neoxelox/HAM/schematics/HAM-BLINDS/ham-blinds_schematic_root.png

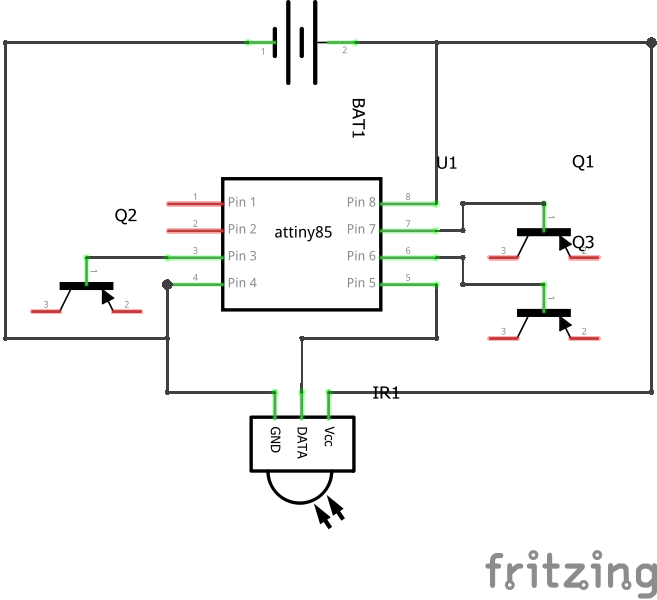
schematics/HAM-BLINDS/ham-blinds_schematic_root.png
