neoxelox/HAM/schematics/HAM-EXT/ham-ext_schematic.png

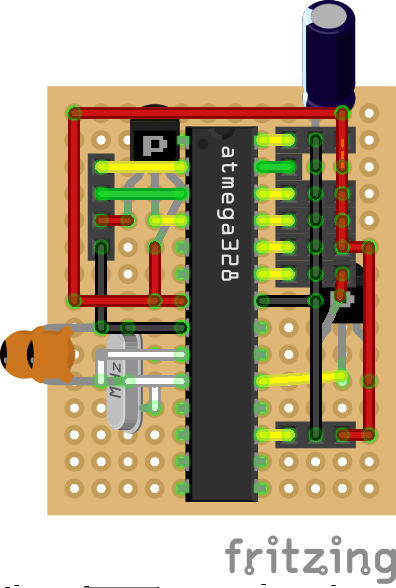
schematics/HAM-EXT/ham-ext_schematic.png
