neoxelox/HAM/schematics/HAM-GAS/ham-gas_schematic.png

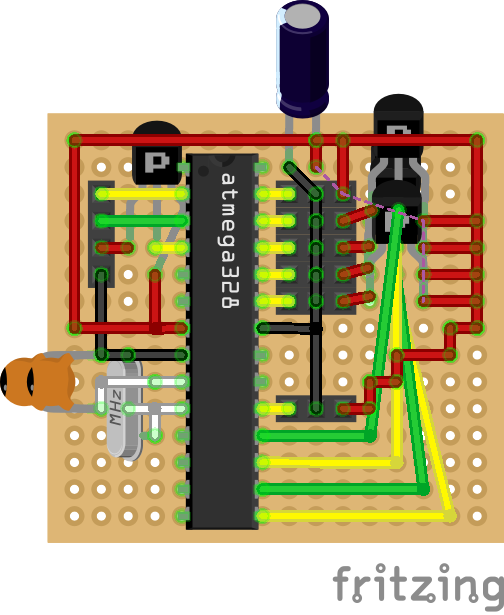
schematics/HAM-GAS/ham-gas_schematic.png
