neoxelox/HAM/schematics/HAM-HUB/ham-hub_schematic-covered.png

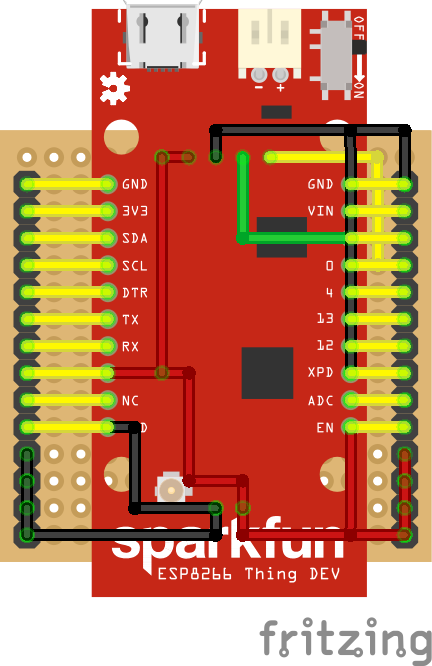
schematics/HAM-HUB/ham-hub_schematic-covered.png
