neoxelox/HAM/schematics/HAM-HUB/ham-hub_schematic-uncovered.png

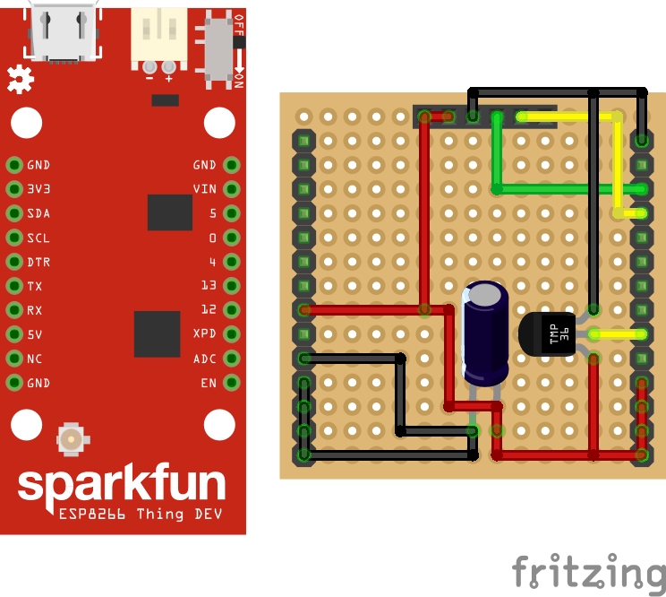
schematics/HAM-HUB/ham-hub_schematic-uncovered.png
