neoxelox/HAM/schematics/HAM-PEEPHOLE/ham-peephole_schematic.png

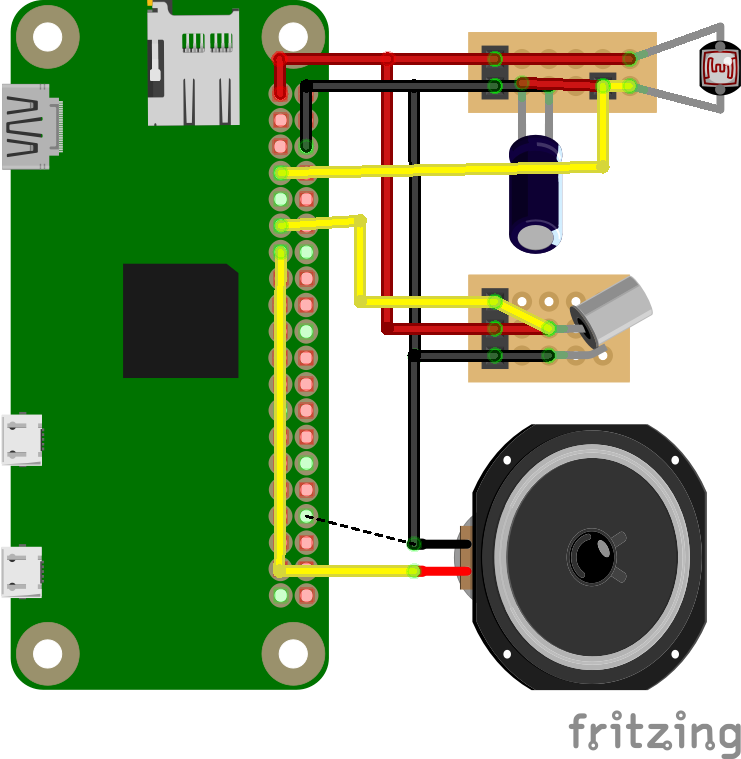
schematics/HAM-PEEPHOLE/ham-peephole_schematic.png
