neoxelox/HAM/schematics/HAM-RDT/ham-rdt_schematic.png

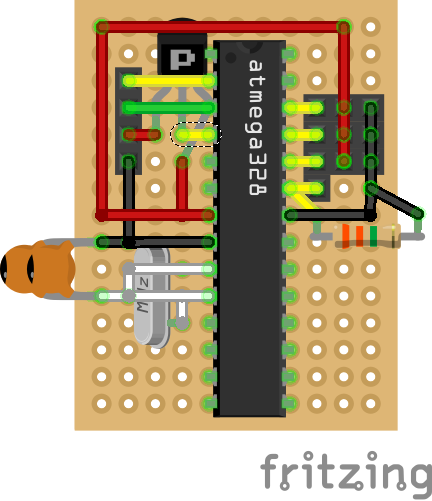
schematics/HAM-RDT/ham-rdt_schematic.png
